y0v1737/chipolino/The_Playbook/pics/lpc1343_2.png

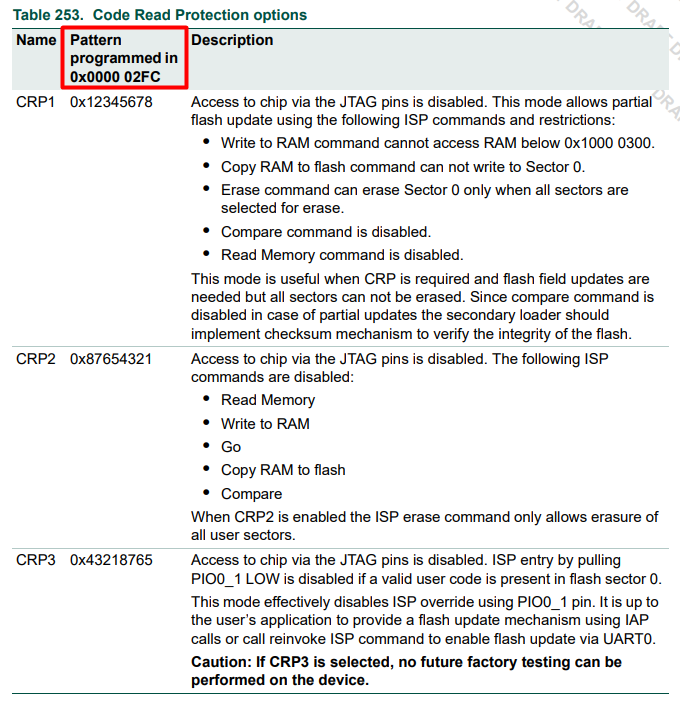
The_Playbook/pics/lpc1343_2.png
