y0v1737/chipolino/The_Playbook/pics/lpc1343_4.png

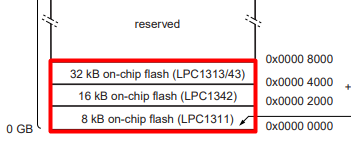
The_Playbook/pics/lpc1343_4.png
