y0v1737/chipolino/The_Playbook/pics/lpc1343_5.png

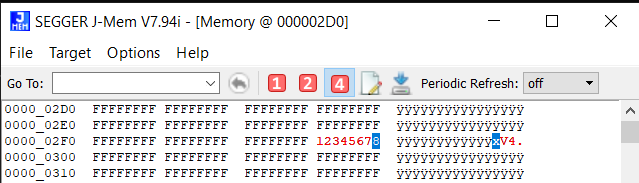
The_Playbook/pics/lpc1343_5.png
