y0v1737/chipolino/The_Playbook/pics/lpc1343_18.png

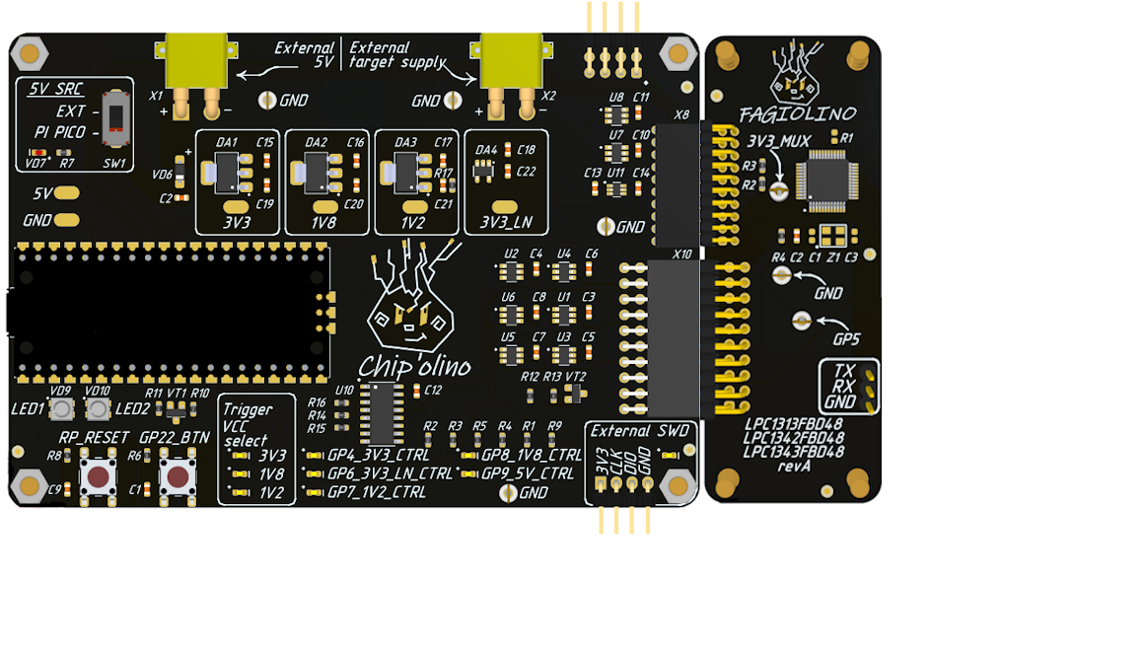
The_Playbook/pics/lpc1343_18.png
