y0v1737/chipolino/The_Playbook/pics/lpc2148_3.png

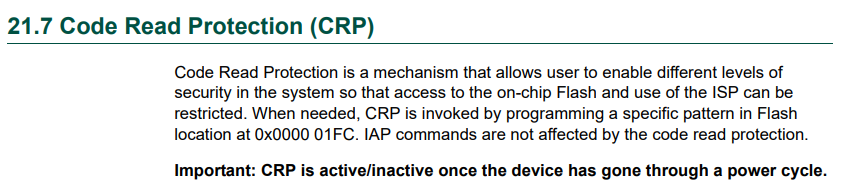
The_Playbook/pics/lpc2148_3.png
