y0v1737/chipolino/The_Playbook/pics/lpc2148_7.png

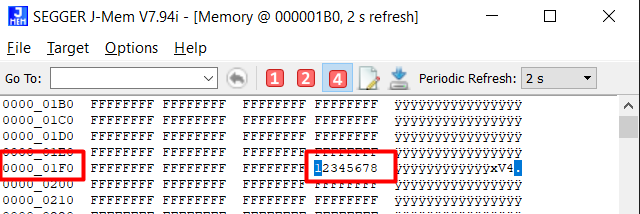
The_Playbook/pics/lpc2148_7.png
