y0v1737/chipolino/The_Playbook/pics/lpc2148_dump_erase.png

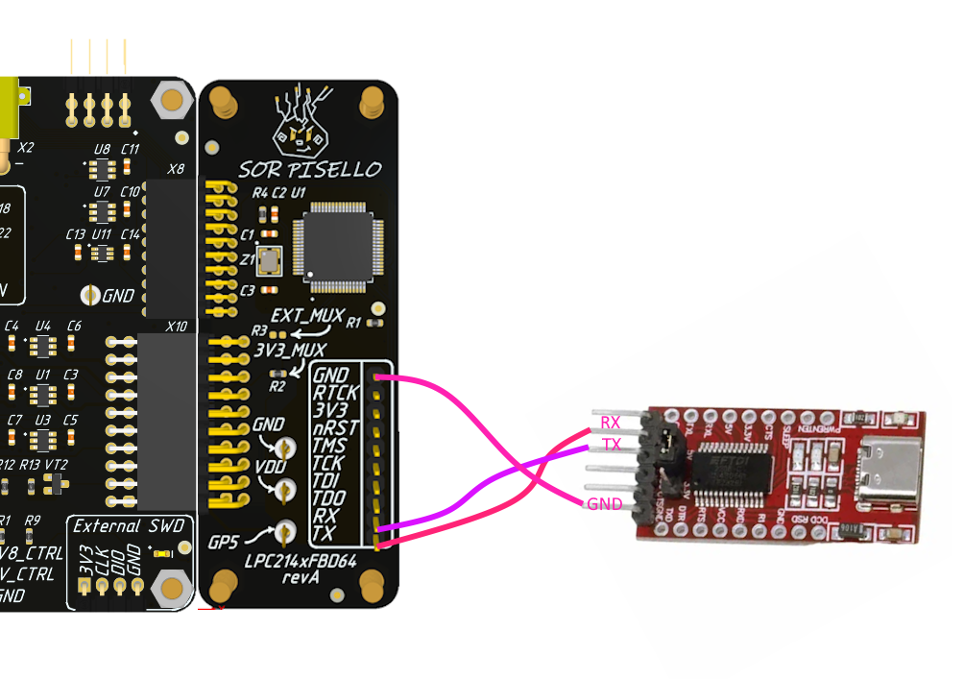
The_Playbook/pics/lpc2148_dump_erase.png
