y0v1737/chipolino/The_Playbook/pics/nrf52833_23.png

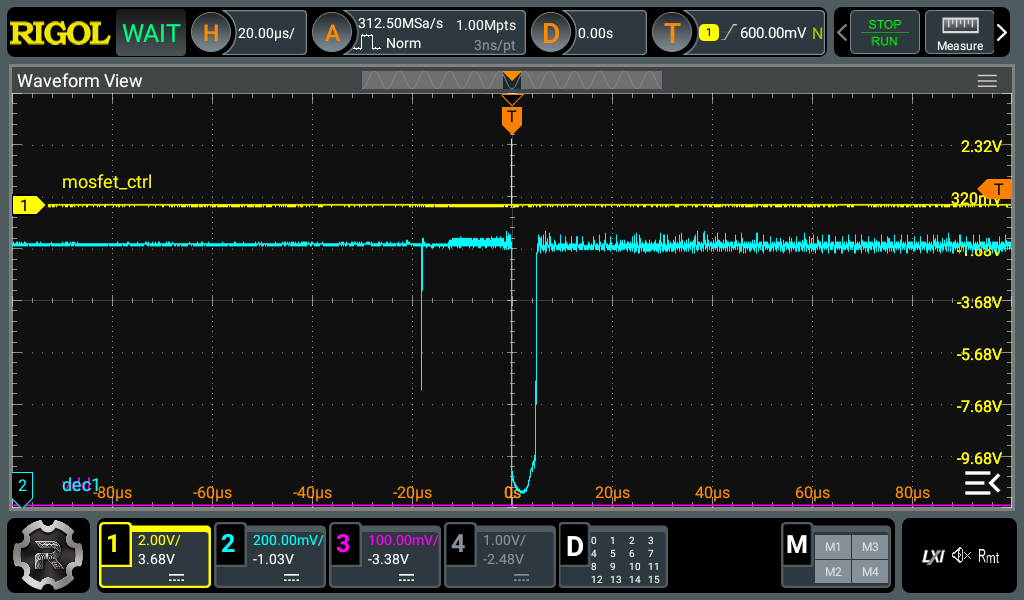
The_Playbook/pics/nrf52833_23.png
