y0v1737/chipolino/The_Playbook/pics/pcb_pics/PATATINA.png

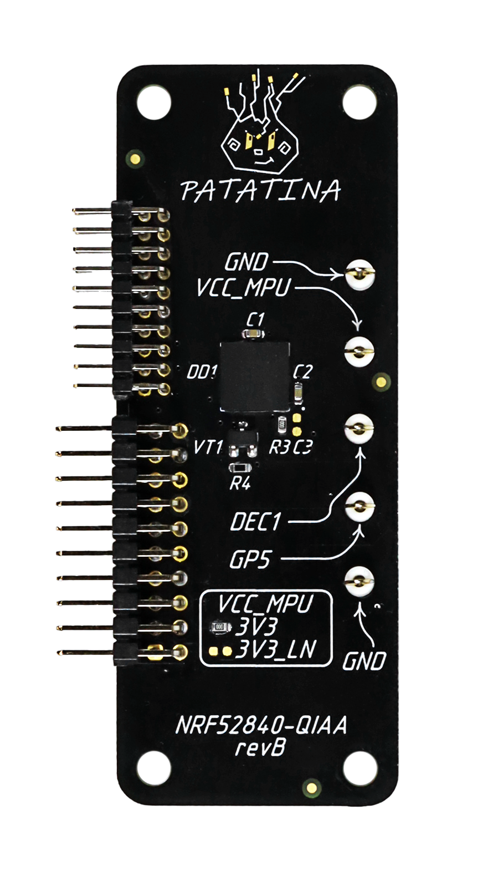
The_Playbook/pics/pcb_pics/PATATINA.png
