y0v1737/chipolino/The_Playbook/pics/pcb_pics/RAVANELLA.png

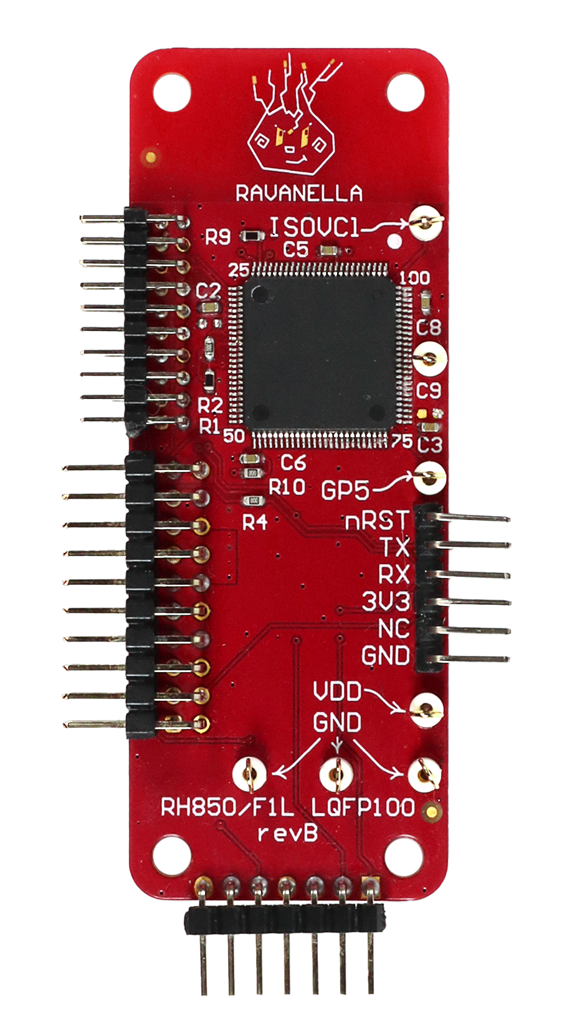
The_Playbook/pics/pcb_pics/RAVANELLA.png
