y0v1737/chipolino/The_Playbook/pics/pcb_pics/STM.png

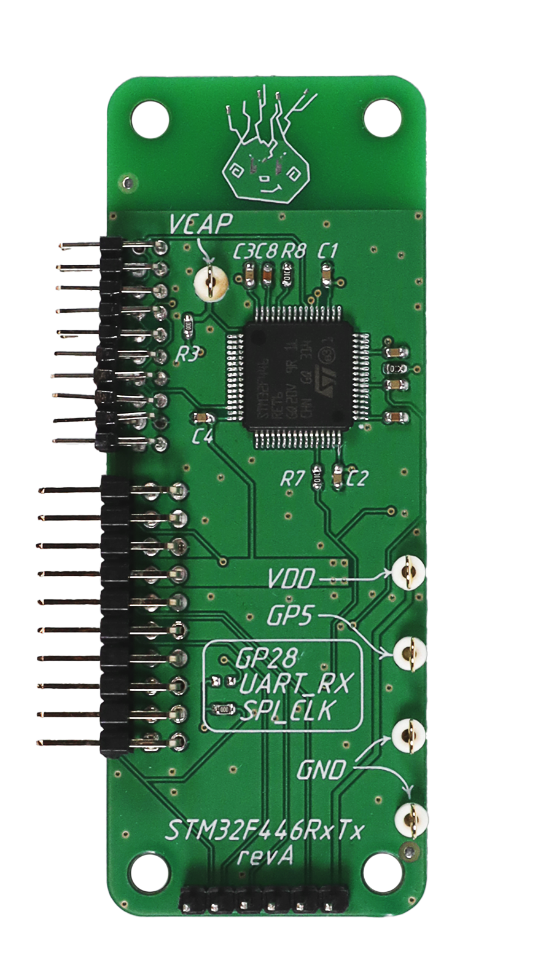
The_Playbook/pics/pcb_pics/STM.png
