y0v1737/chipolino/The_Playbook/pics/rh850_5.JPG

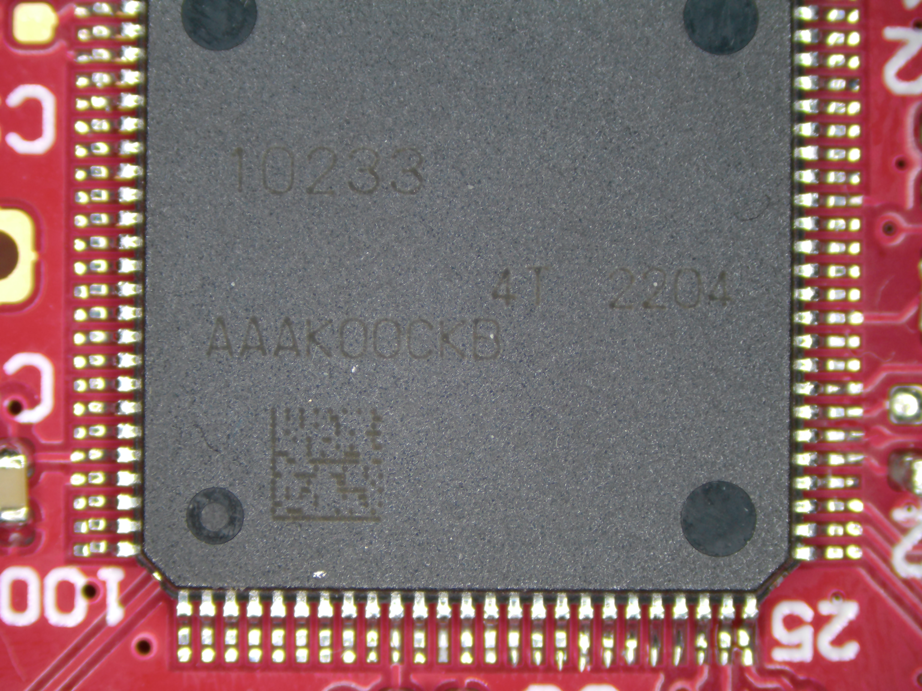
The_Playbook/pics/rh850_5.JPG
