y0v1737/chipolino/The_Playbook/pics/rh850_29.png

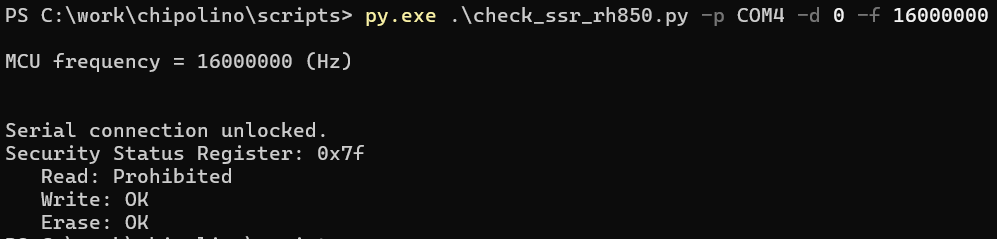
The_Playbook/pics/rh850_29.png
