y0v1737/chipolino/The_Playbook/pics/rh850_40.png

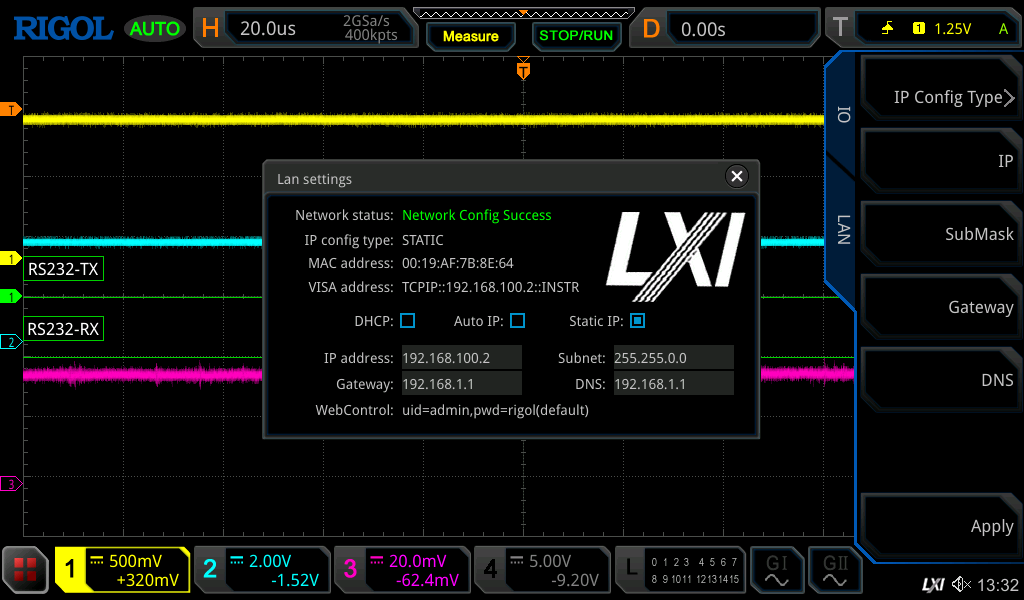
The_Playbook/pics/rh850_40.png
