y0v1737/chipolino/The_Playbook/pics/rk3588/rk3588_1.png

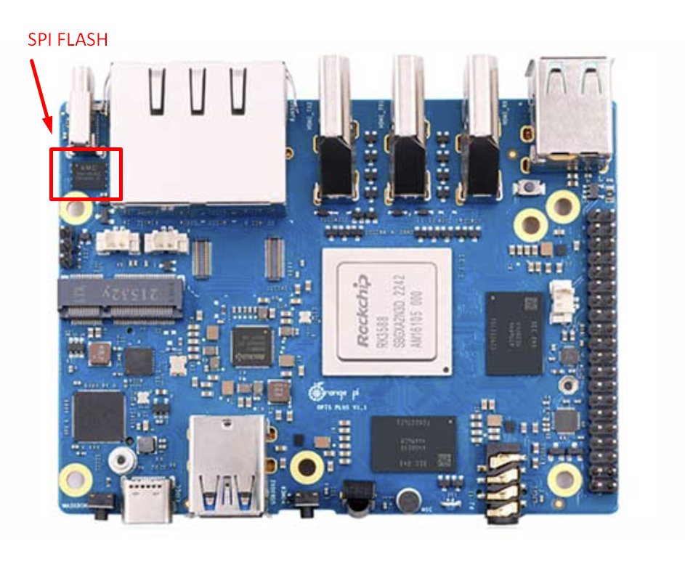
The_Playbook/pics/rk3588/rk3588_1.png
