y0v1737/chipolino/The_Playbook/pics/rtl8762c_11.png

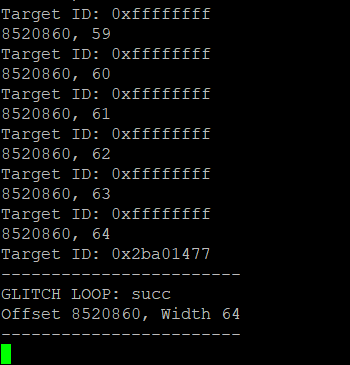
The_Playbook/pics/rtl8762c_11.png
