y0v1737/chipolino/The_Playbook/pics/stm32f411_15.png

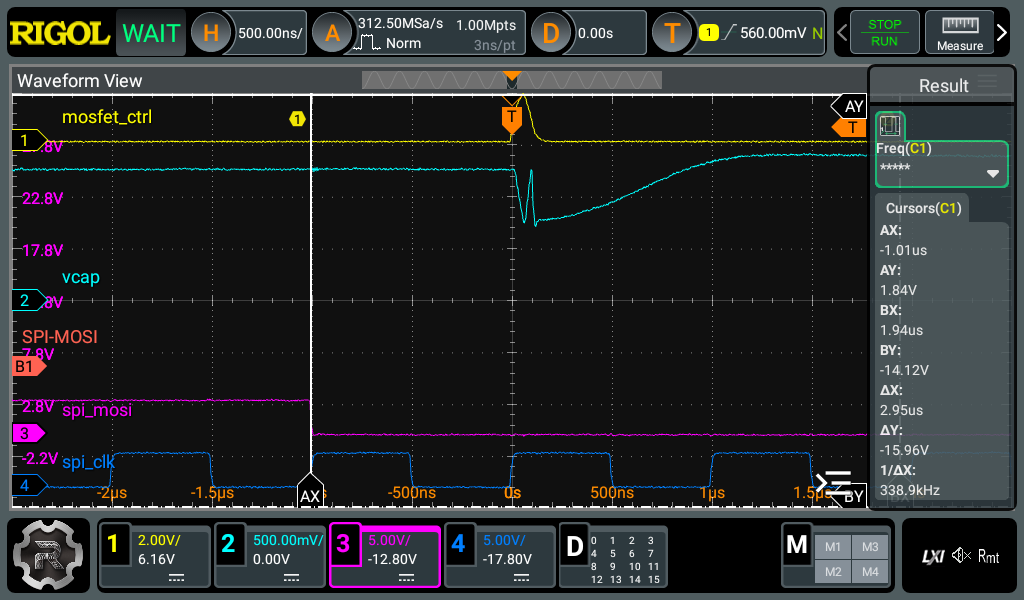
The_Playbook/pics/stm32f411_15.png
