y0v1737/chipolino/The_Playbook/pics/stm32f429_6.png

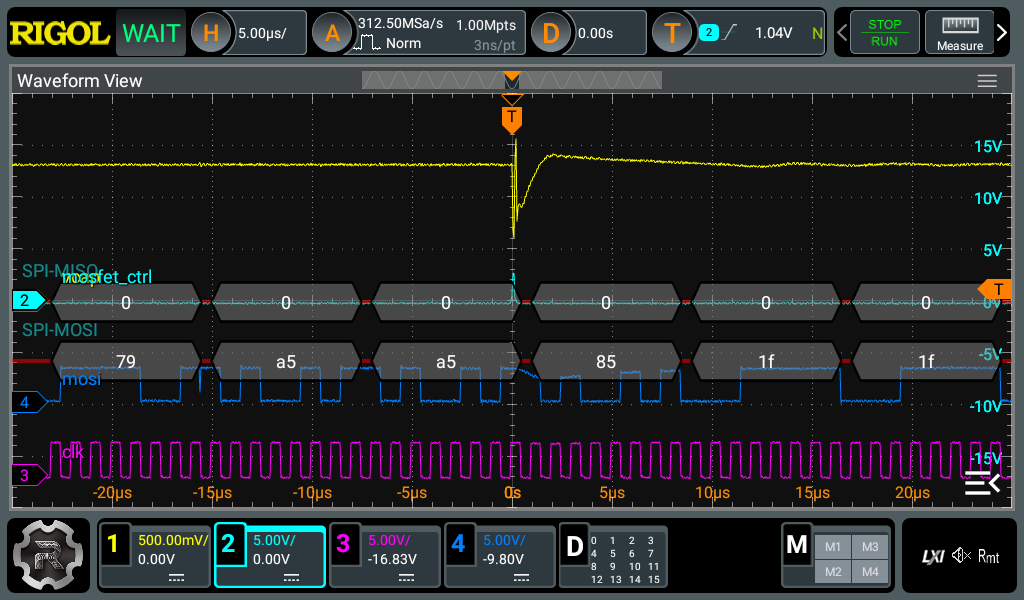
The_Playbook/pics/stm32f429_6.png
