y0v1737/chipolino/The_Playbook/pics/stm32f429_8.png

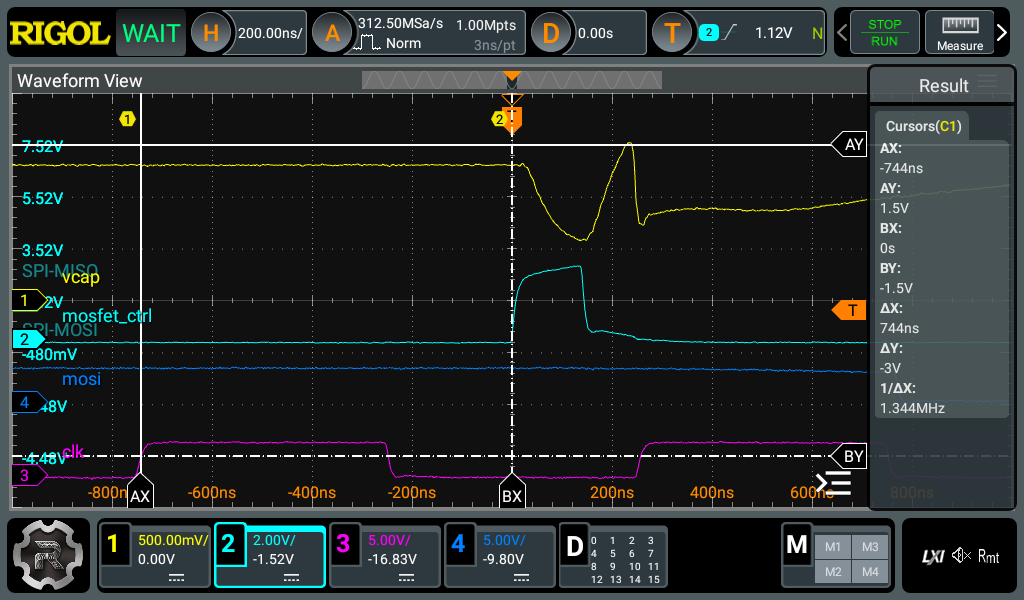
The_Playbook/pics/stm32f429_8.png
