y0v1737/chipolino/The_Playbook/pics/stm32f429_10.png

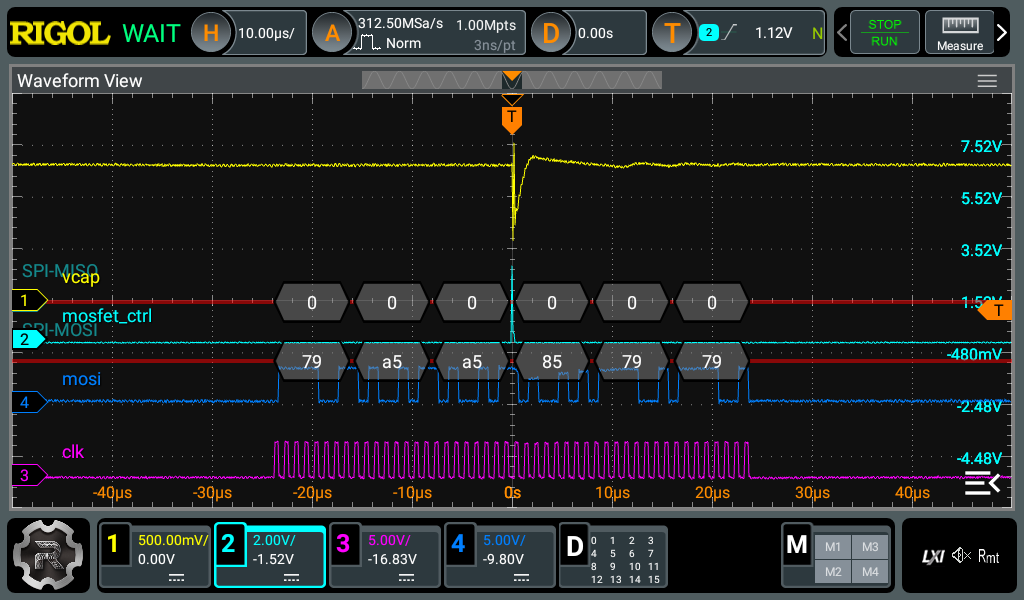
The_Playbook/pics/stm32f429_10.png
