y0v1737/chipolino/The_Playbook/pics/stm32f466_49.png

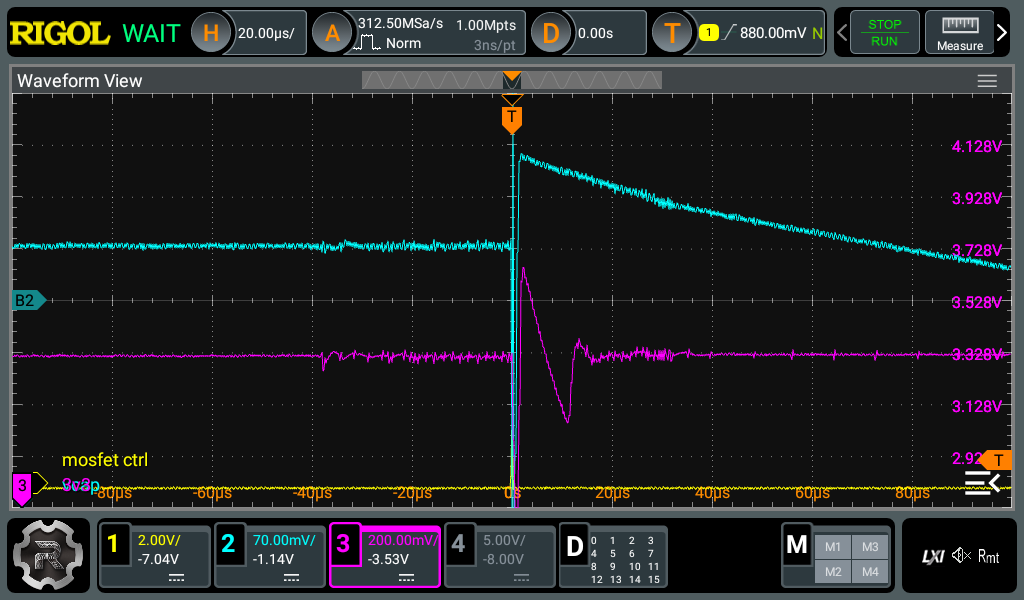
The_Playbook/pics/stm32f466_49.png
