y0v1737/chipolino/The_Playbook/pics/rh850_check_protect_setup.png

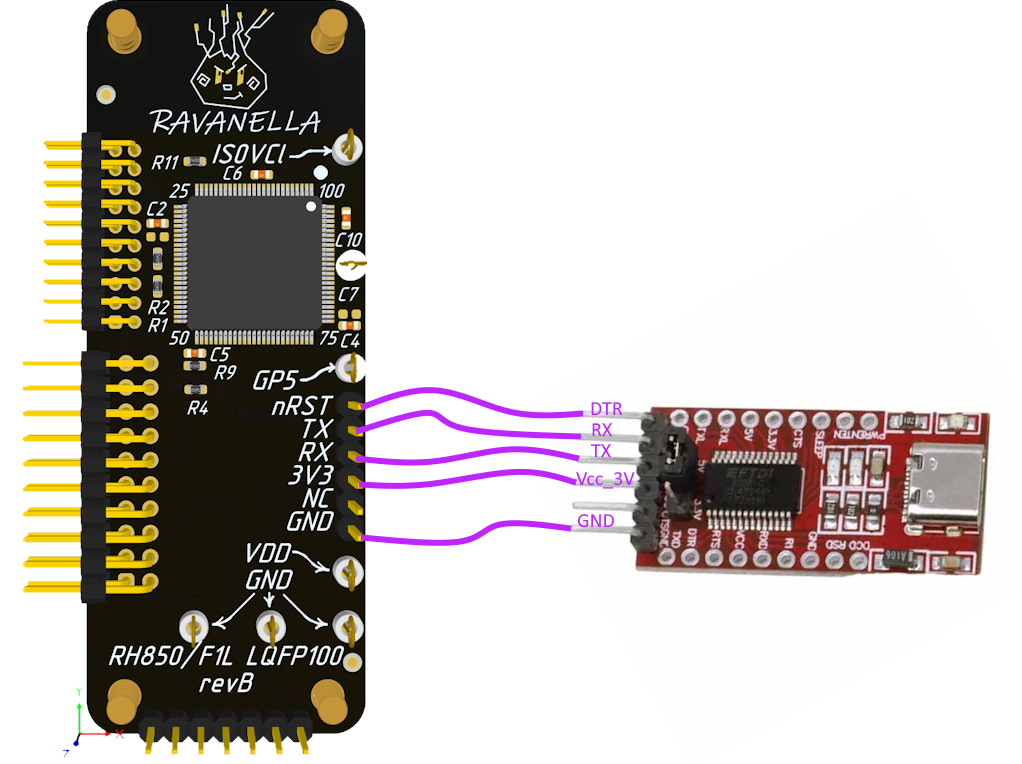
The_Playbook/pics/rh850_check_protect_setup.png
