y0v1737/chipolino/pcb/Addons/STM/STM32F411CCU_revA/Schematic PDF/STM32F411CCU_revA.PDF

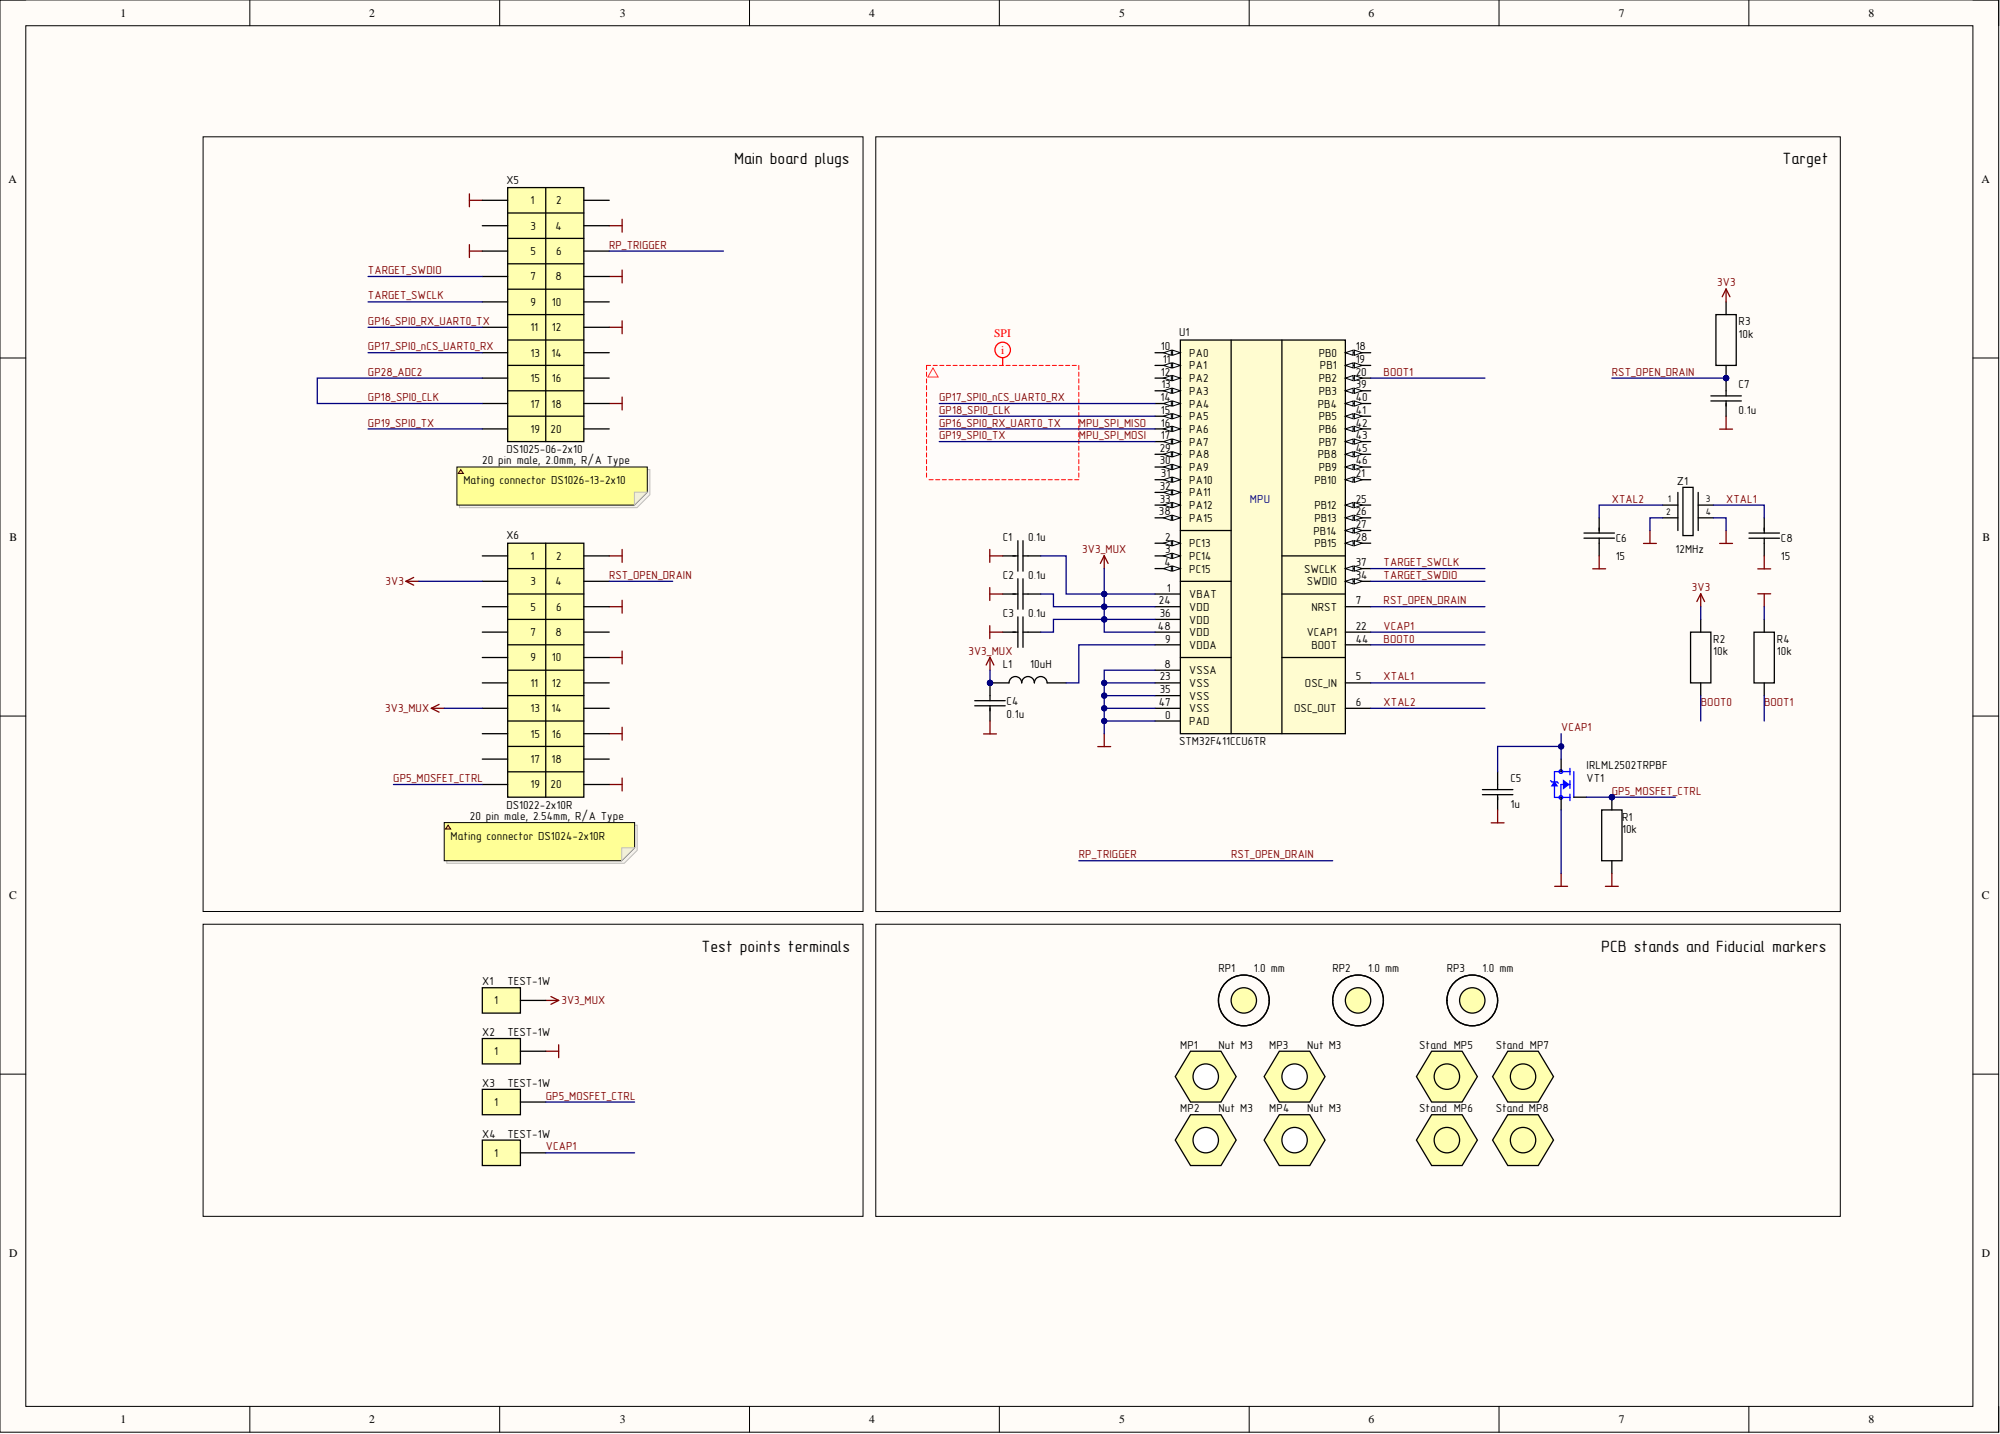
[picture p253: page 1]

VDD 36

PCB stands and Fiducial markers
