y0v1737/chipolino/pcb/Addons/Realtek/RTL8762CKF/RTL8762CKF_revA/Schematic PDF/RTL8762CKF_revA.PDF

4 | RST_OPEN_DRAIN 3

PCB stands and Fiducial markers
