y0v1737/chipolino/pcb/Addons/Nordic/nRF52832-CIAA/nRF52832-CIAA_revC/Schematic PDF/nRF52832-CIAA_revC for assembly.PDF

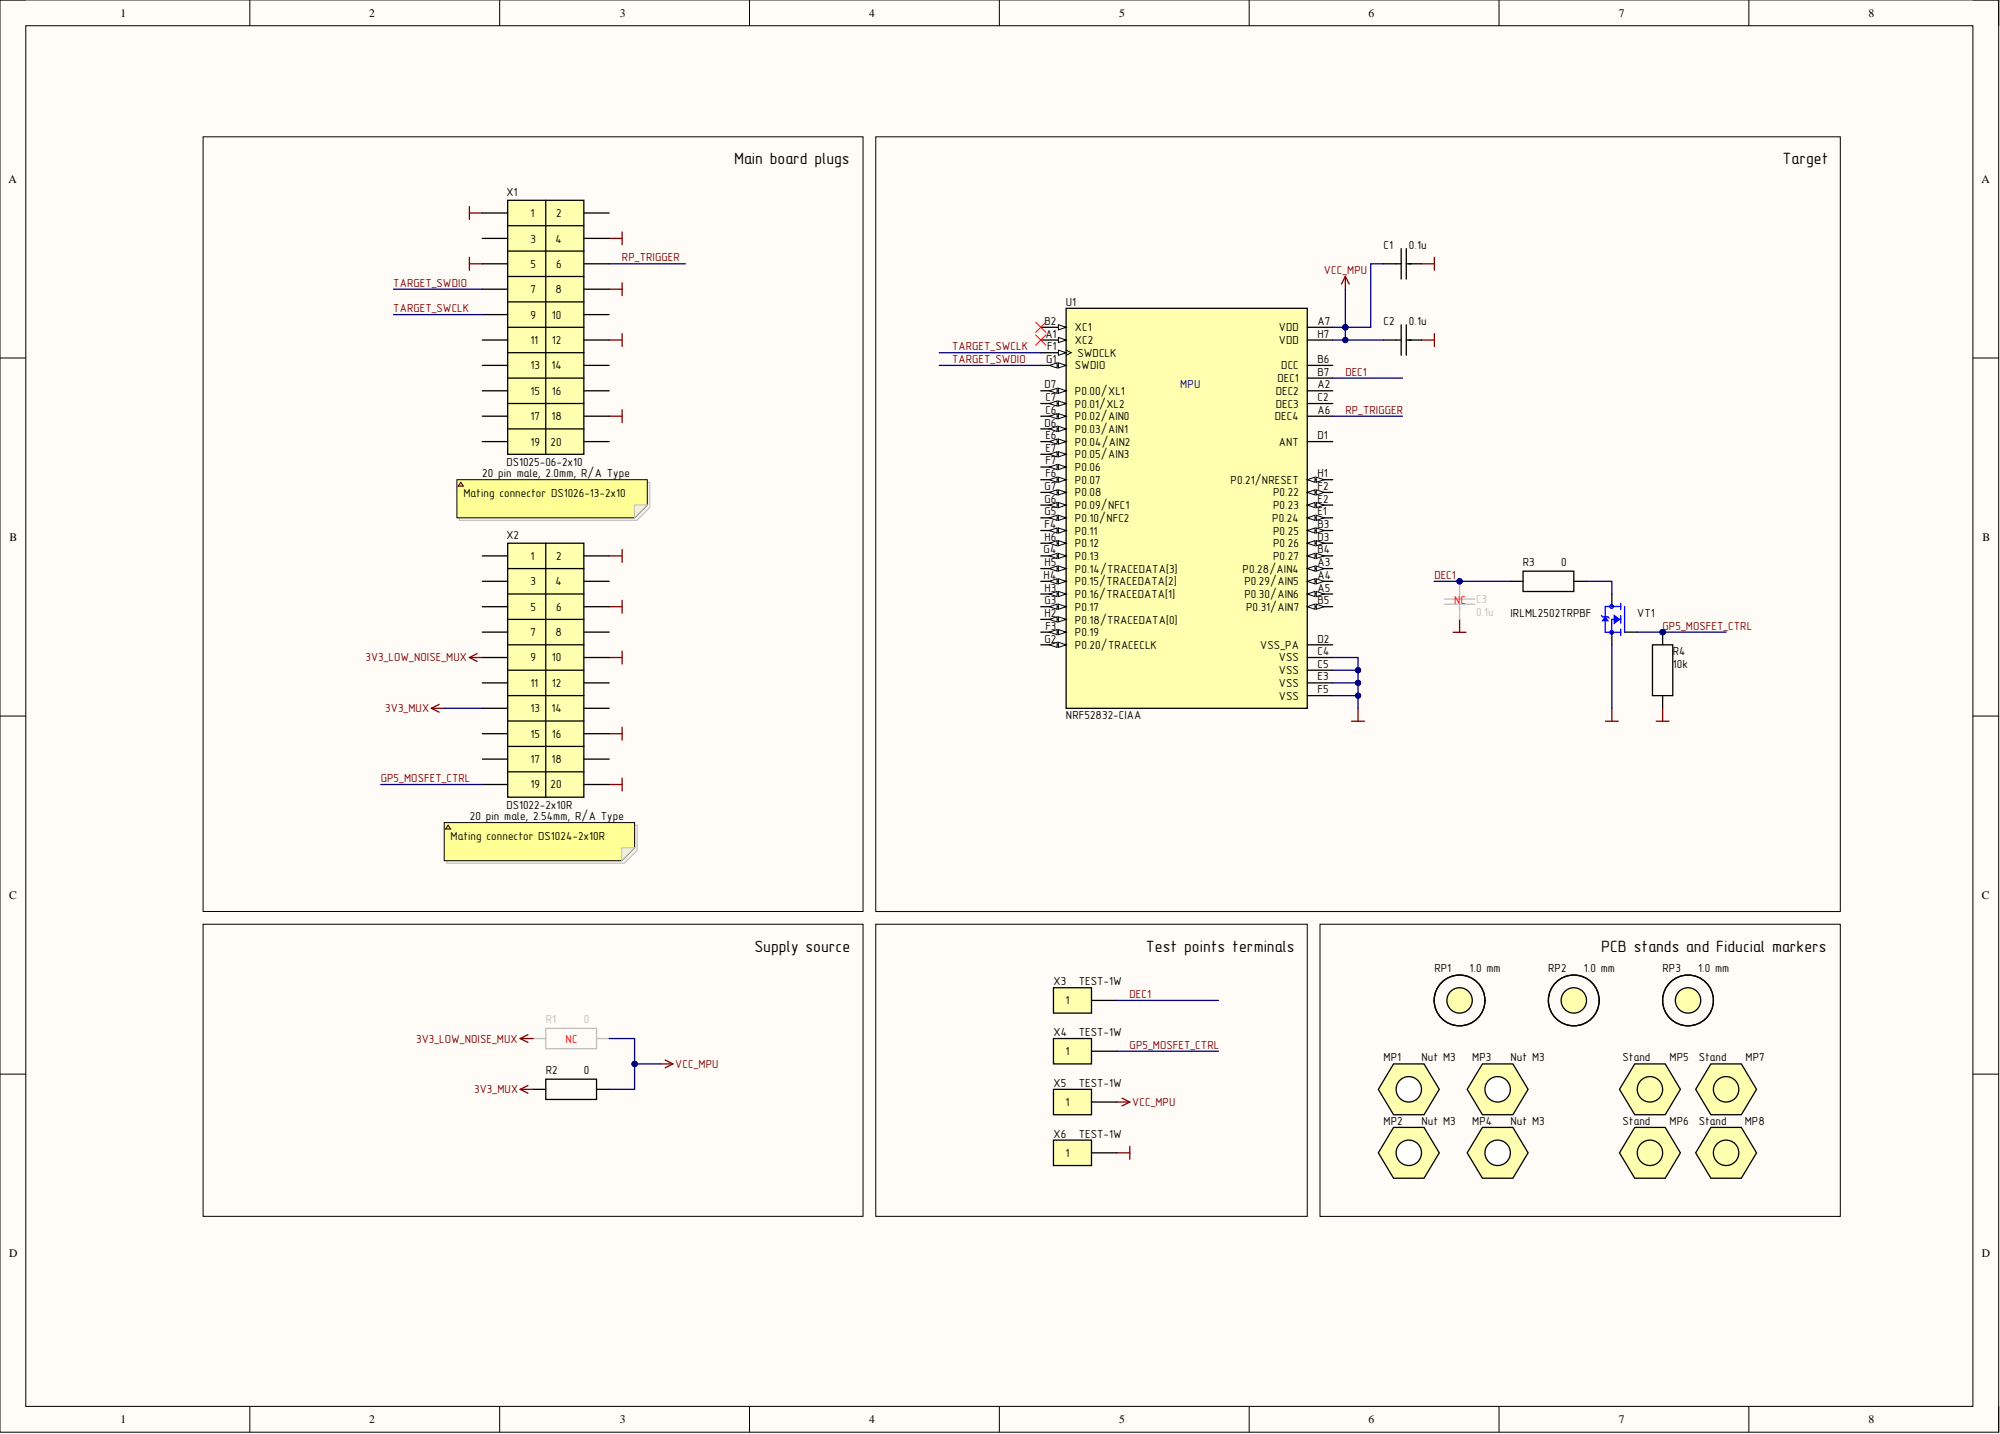
[picture p255: page 1]

PCB stands and Fiducial markers
