y0v1737/chipolino/pcb/Addons/Nordic/nRF52833-QDAA/nRF52833-QDAA_revC/Schematic PDF/nRF52833-QDAA_revC for assembly.PDF

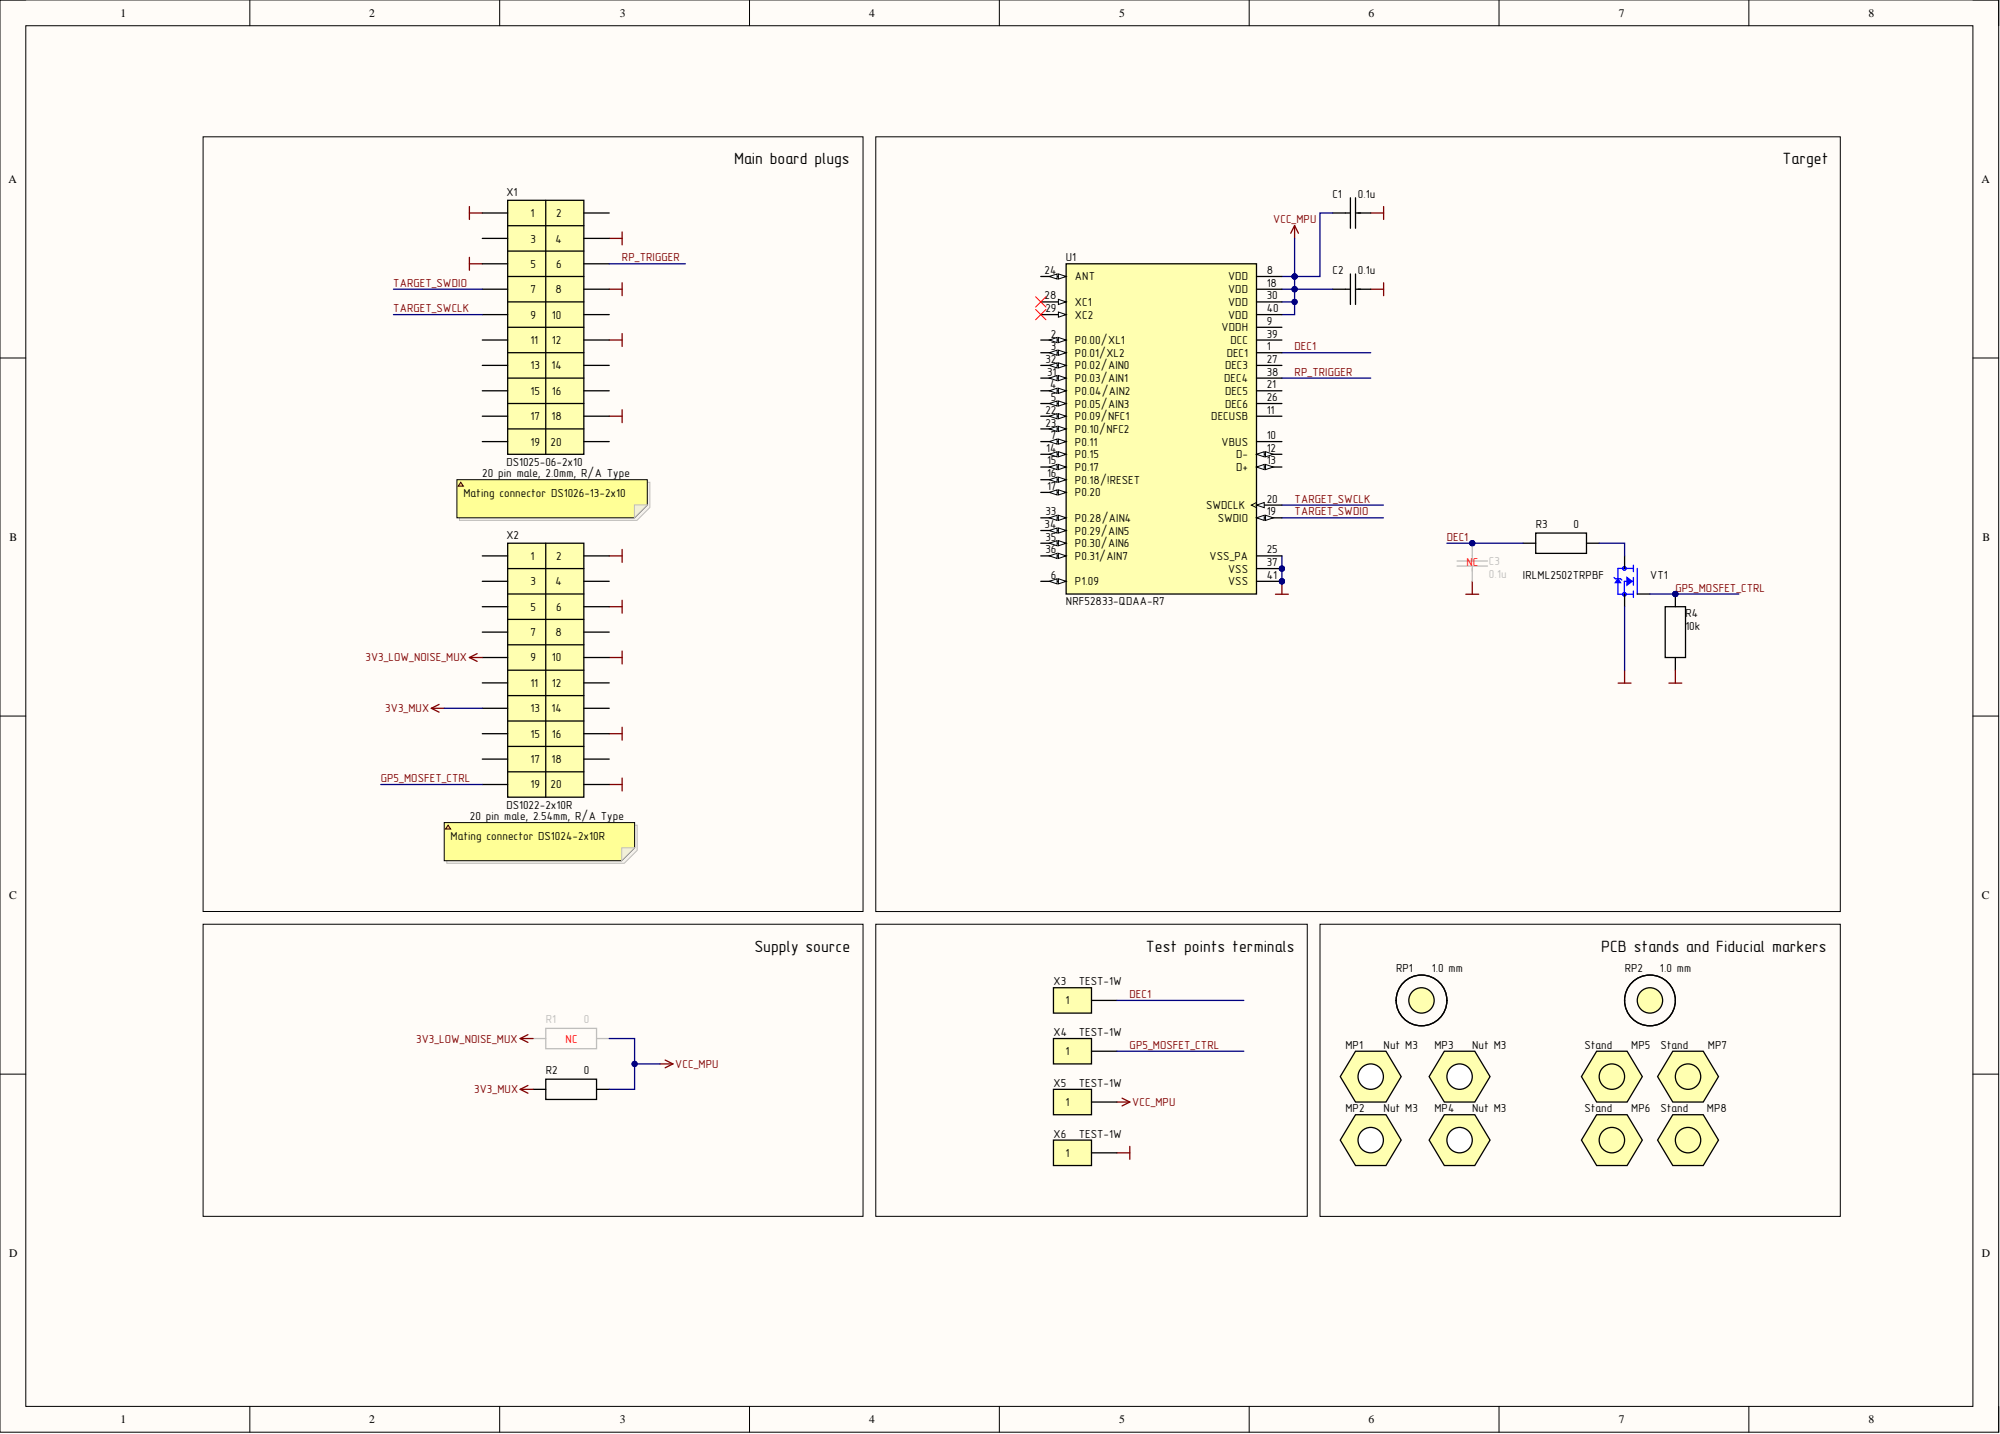
[picture p257: page 1]

PCB stands and Fiducial markers
