y0v1737/chipolino/pcb/Addons/Nordic/nRF52833-QDAA/nRF52833-QDAA_revC/Schematic PDF/nRF52833-QDAA_revC.PDF

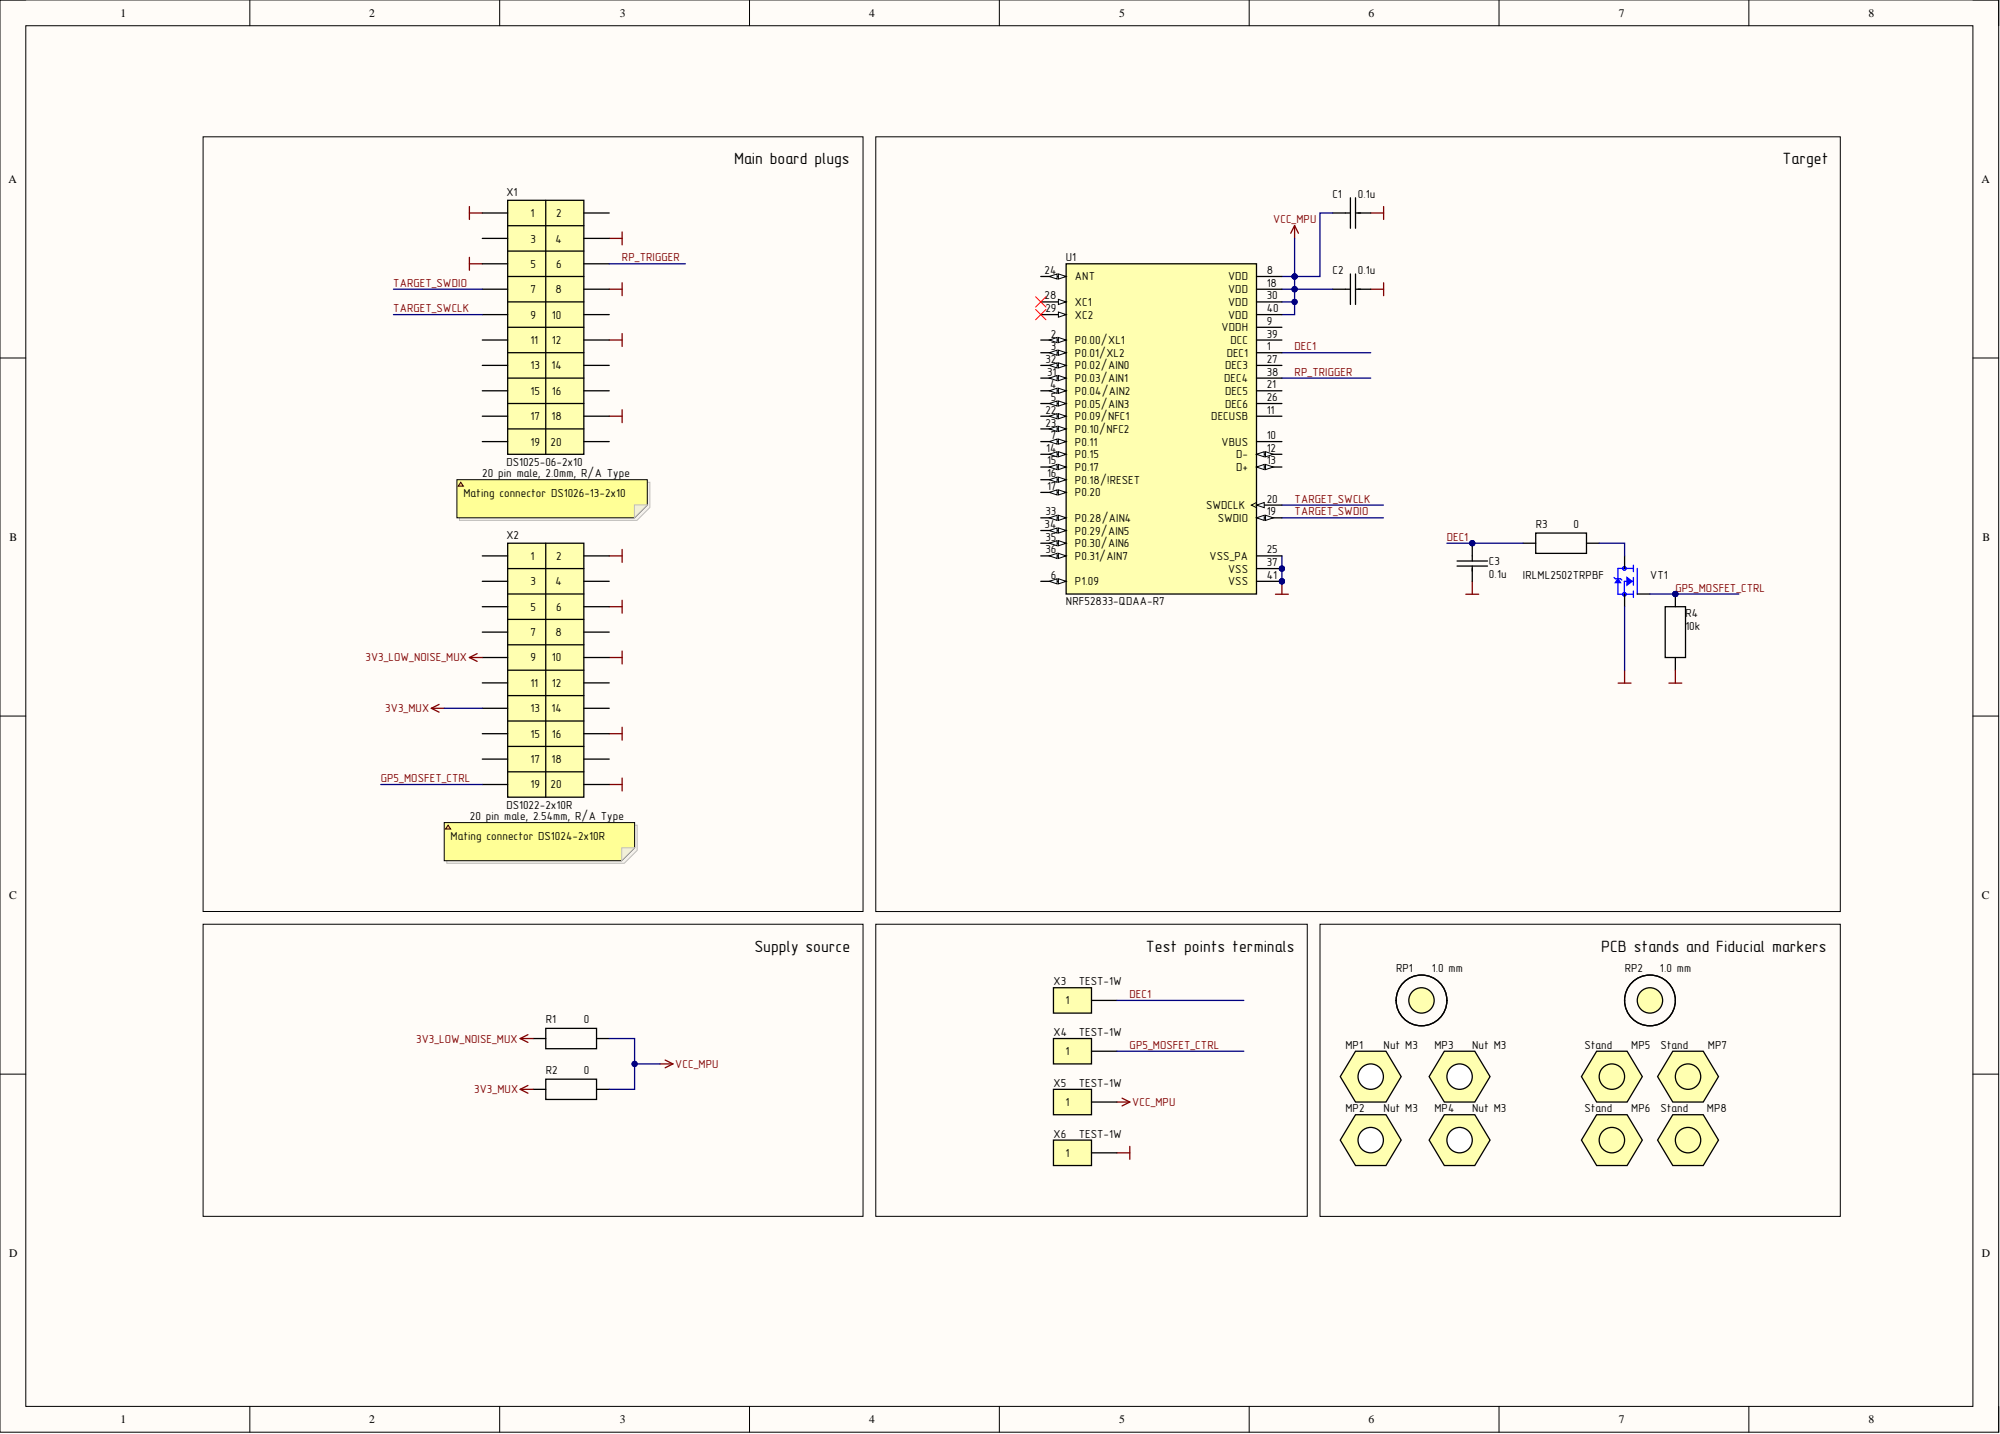
[picture p258: page 1]

PCB stands and Fiducial markers
