y0v1737/chipolino/pcb/Addons/Nordic/nRF52840-QIAA/nRF52840-QIAA_revB/Schematic PDF/nRF52840-QIAA_revB for assembly.PDF

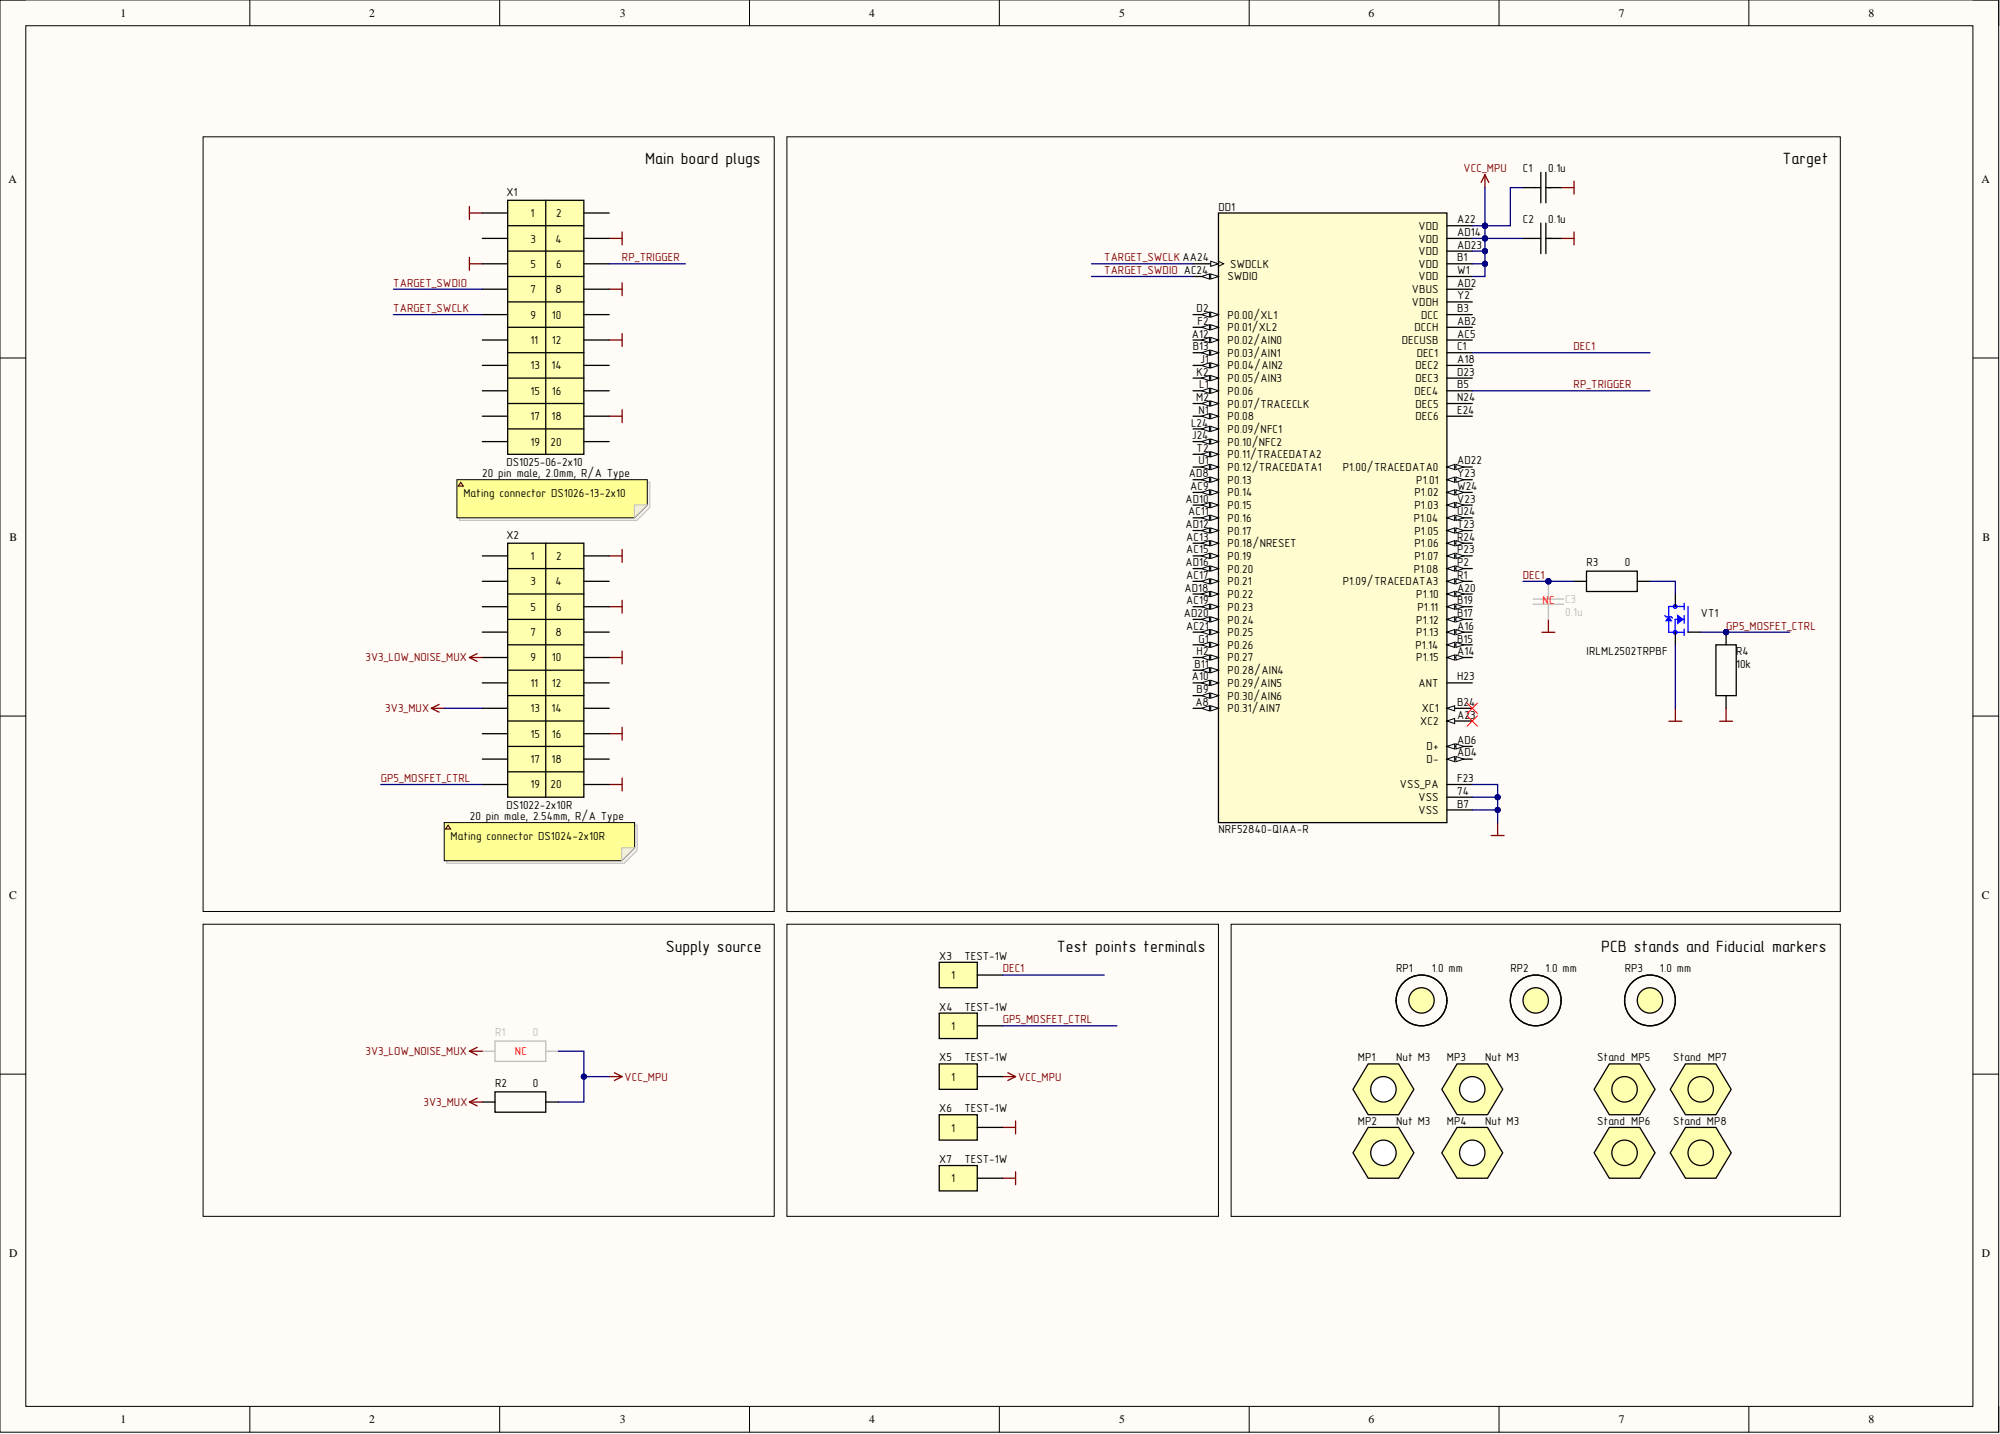
[picture p259: page 1]

PCB stands and Fiducial markers
