y0v1737/chipolino/The_Playbook/Chipolino_logic_sch/Chipolino_logic_sch.pdf

3V3, 1V8, 1V2,
5V

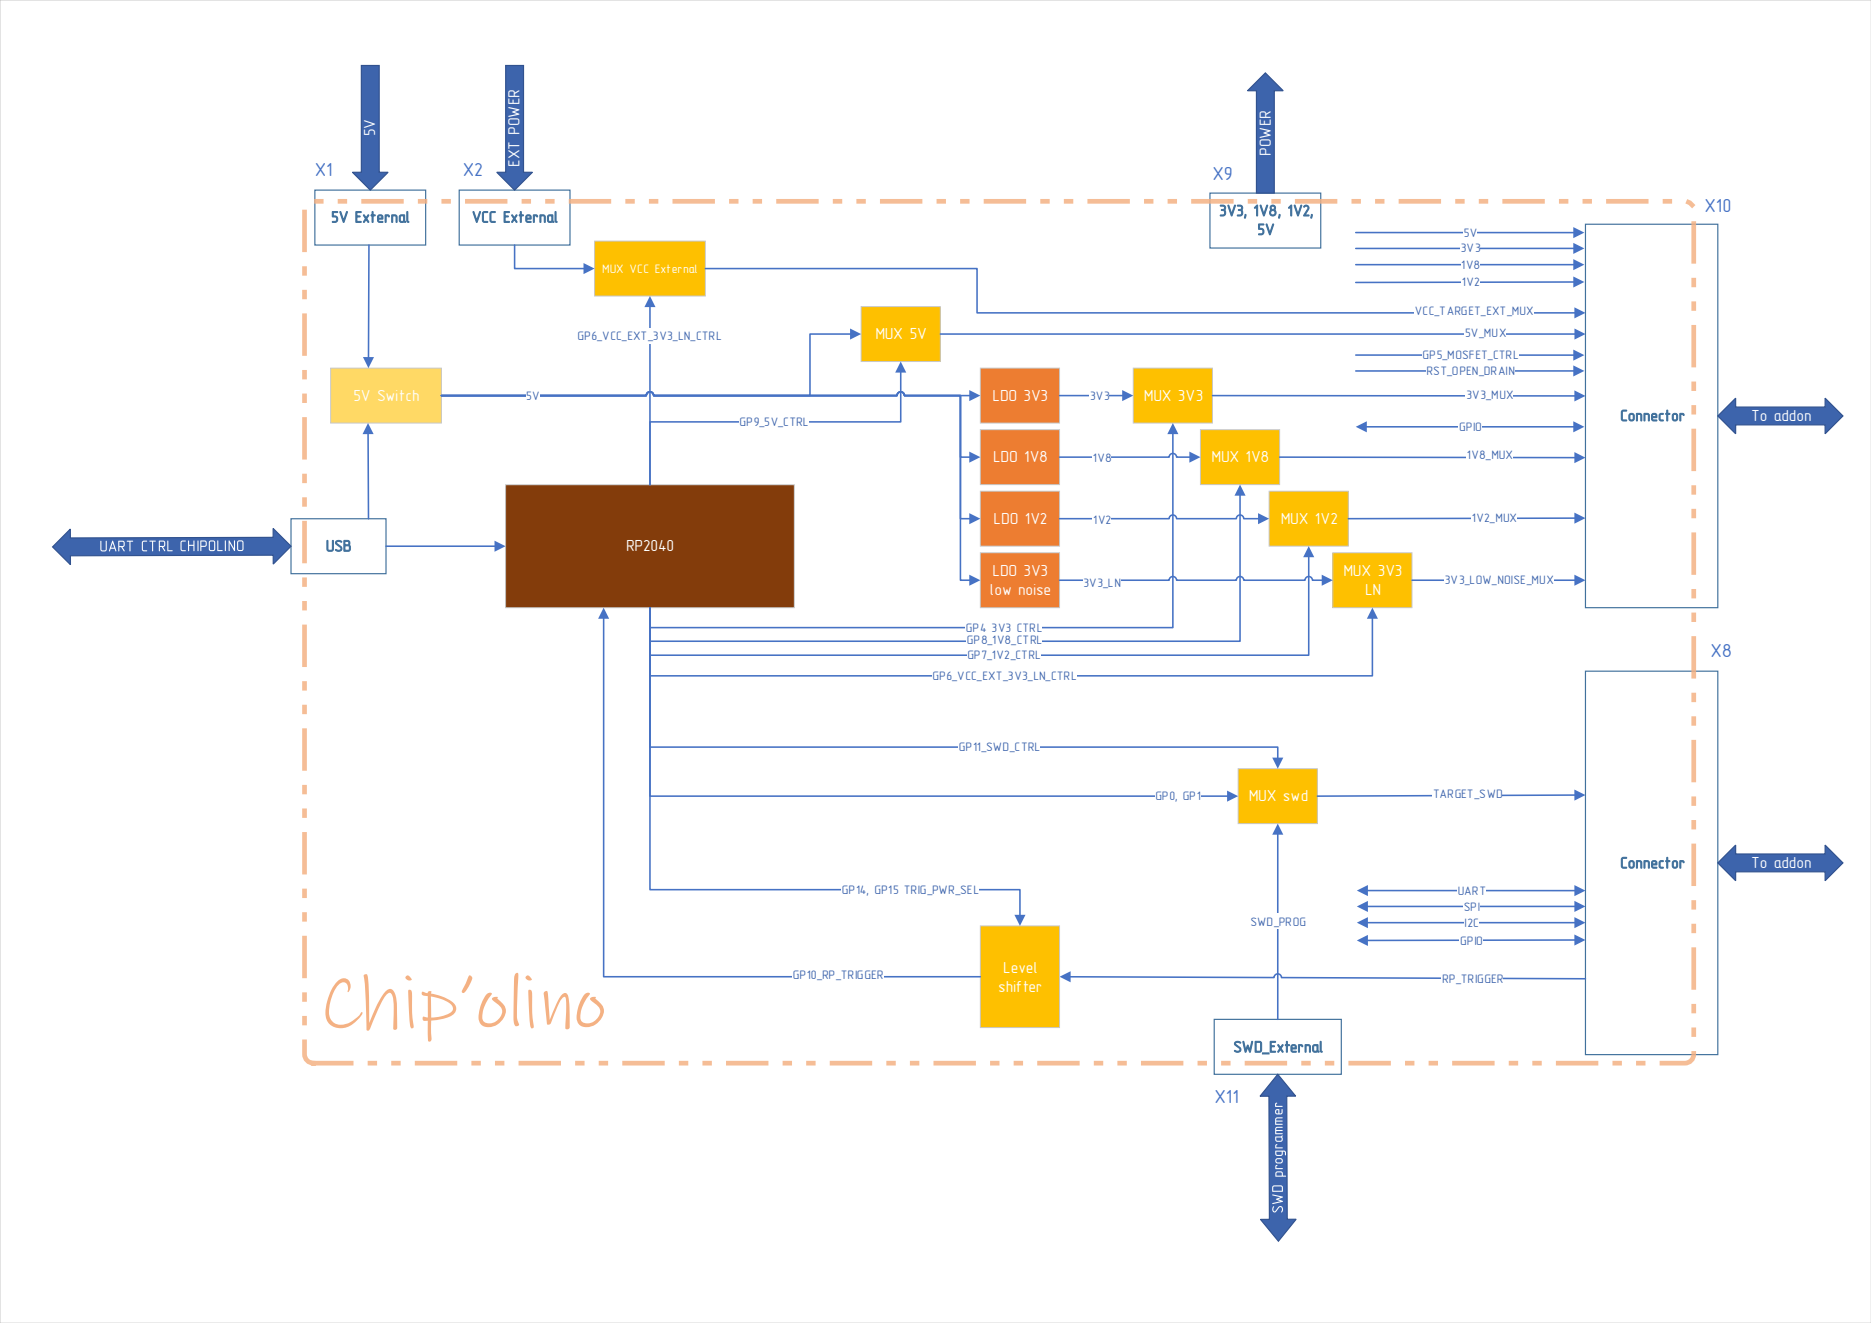
[picture p261: page 1]
MUX 3V3; MUX 1V8; LDO 3V3; LDO 1V8; LDO 1V2; LDO 3V3 low noise; MUX 1V2; MUX 3V3 LN; GP6_VCC_EXT_3V3_LN_CTRL; USB; 5V External; VCC External; 5V Switch; Connector; SWD_External; MUX swd; SWD_PROG; GP11_SWD_CTRL; TARGET_SWD; UART SPI; GPIO; RP_TRIGGER; MUX 5V; GP9_5V_CTRL; Level shifter; GP10_RP_TRIGGER; GP14, GP15 TRIG_PWR_SEL; EXT POWER; To addon; POWER; 3V3_MUX; 1V8_MUX; 1V2_MUX; 3V3_LOW_NOISE_MUX; 5V_MUX; GP5_MOSFET_CTRL RST_OPEN_DRAIN; VCC_TARGET_EXT_MUX; Chip’olino

MUX VCC External

GP4_3V3_CTRL
GP8_1V8_CTRL
GP7_1V2_CTRL
